chrisjrob/gokart-repair/IMAG0990.jpg

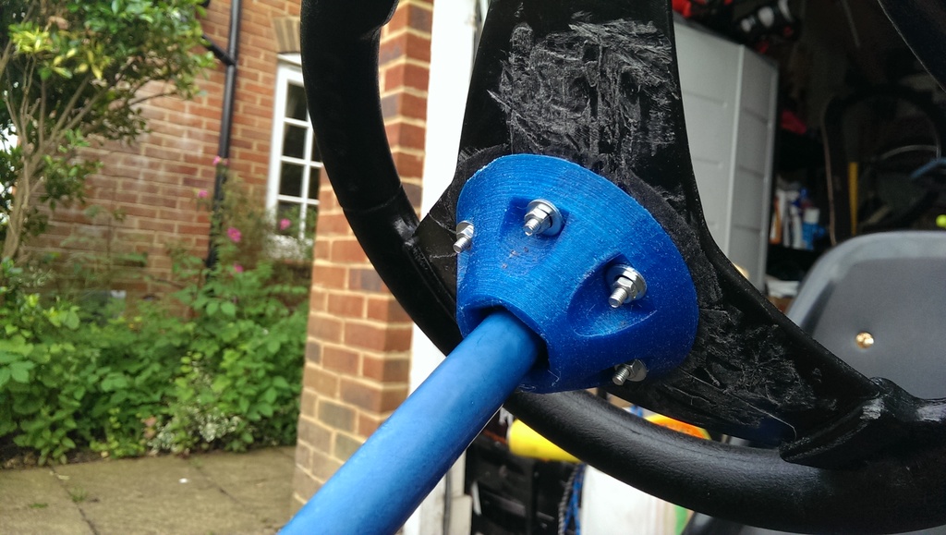
IMAG0990.jpg
