chrisjrob/gokart-repair/IMAG0991.jpg

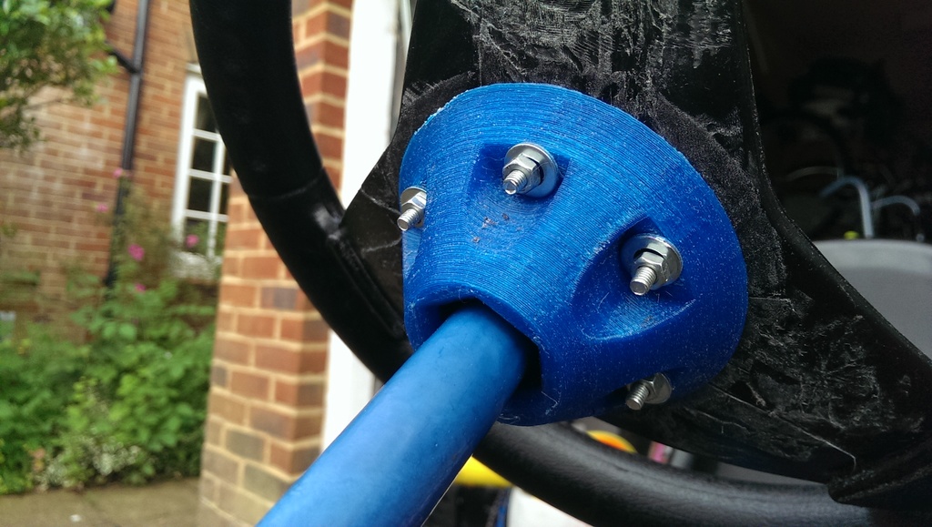
IMAG0991.jpg
