chrisjrob/gokart-repair/IMAG0992.jpg

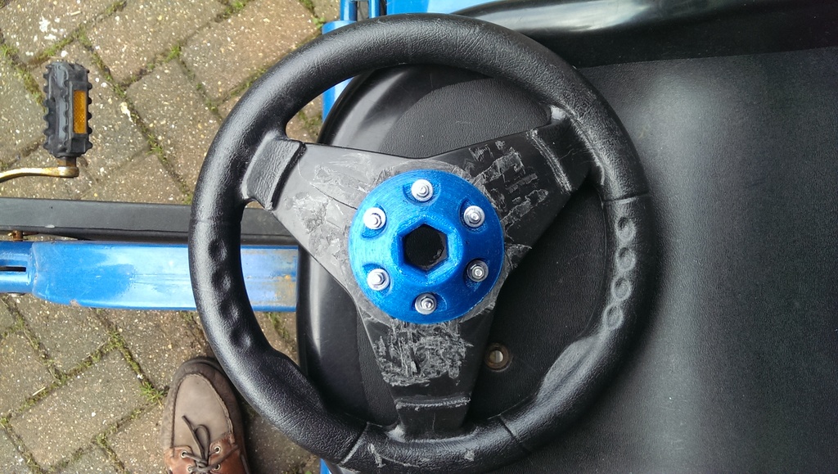
IMAG0992.jpg
