chrisjrob/gokart-repair/IMAG0993.jpg

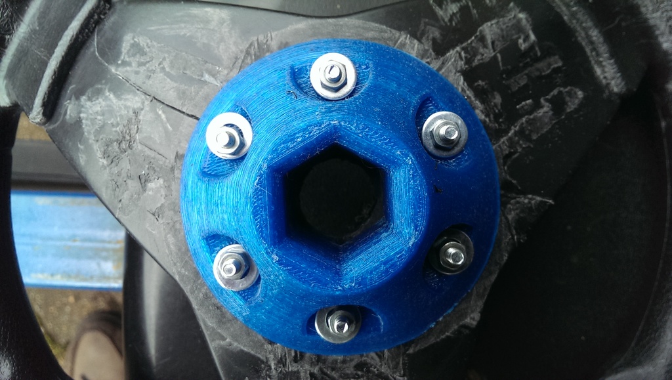
IMAG0993.jpg
