chrisjrob/gokart-repair/IMAG0995.jpg

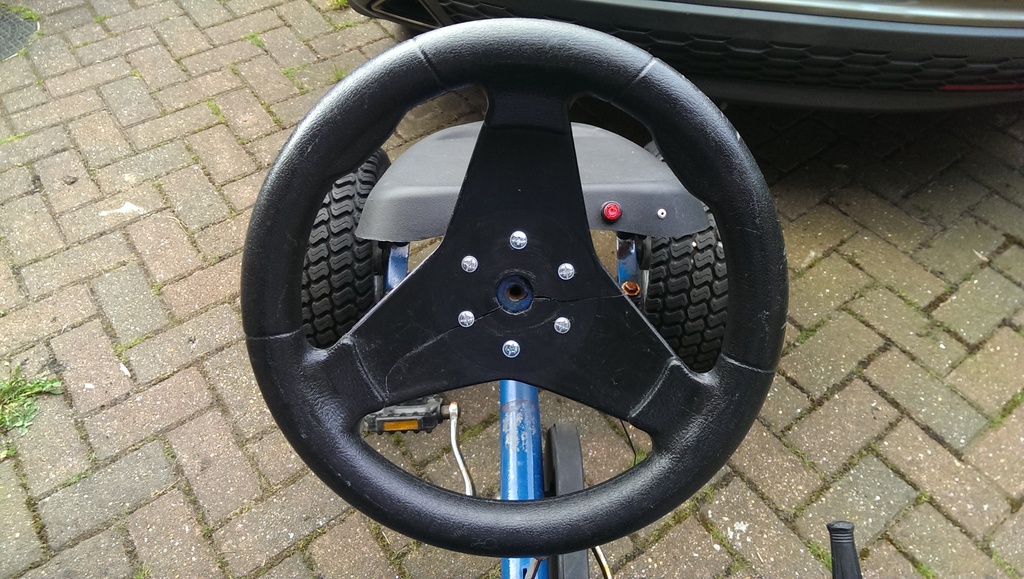
IMAG0995.jpg
