chrisjrob/gokart-repair/gokart-repair.png

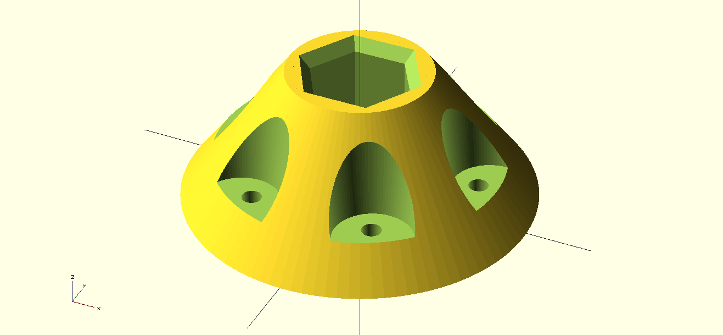
gokart-repair.png
